ScatteredDrifter/Buran-Ortho/images/top-options/buran_top_filled.PNG

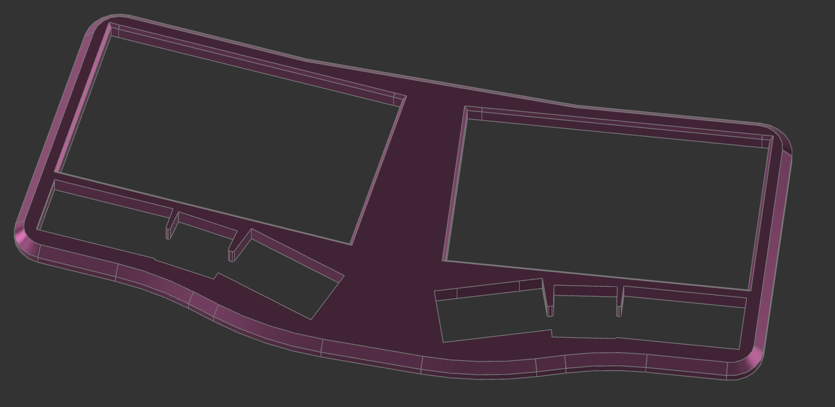
images/top-options/buran_top_filled.PNG
