ScatteredDrifter/Buran-Ortho/pcb/knobdeavour.kicad_sch

## KiCad design pcb/knobdeavour.kicad_sch (2022-11-30)

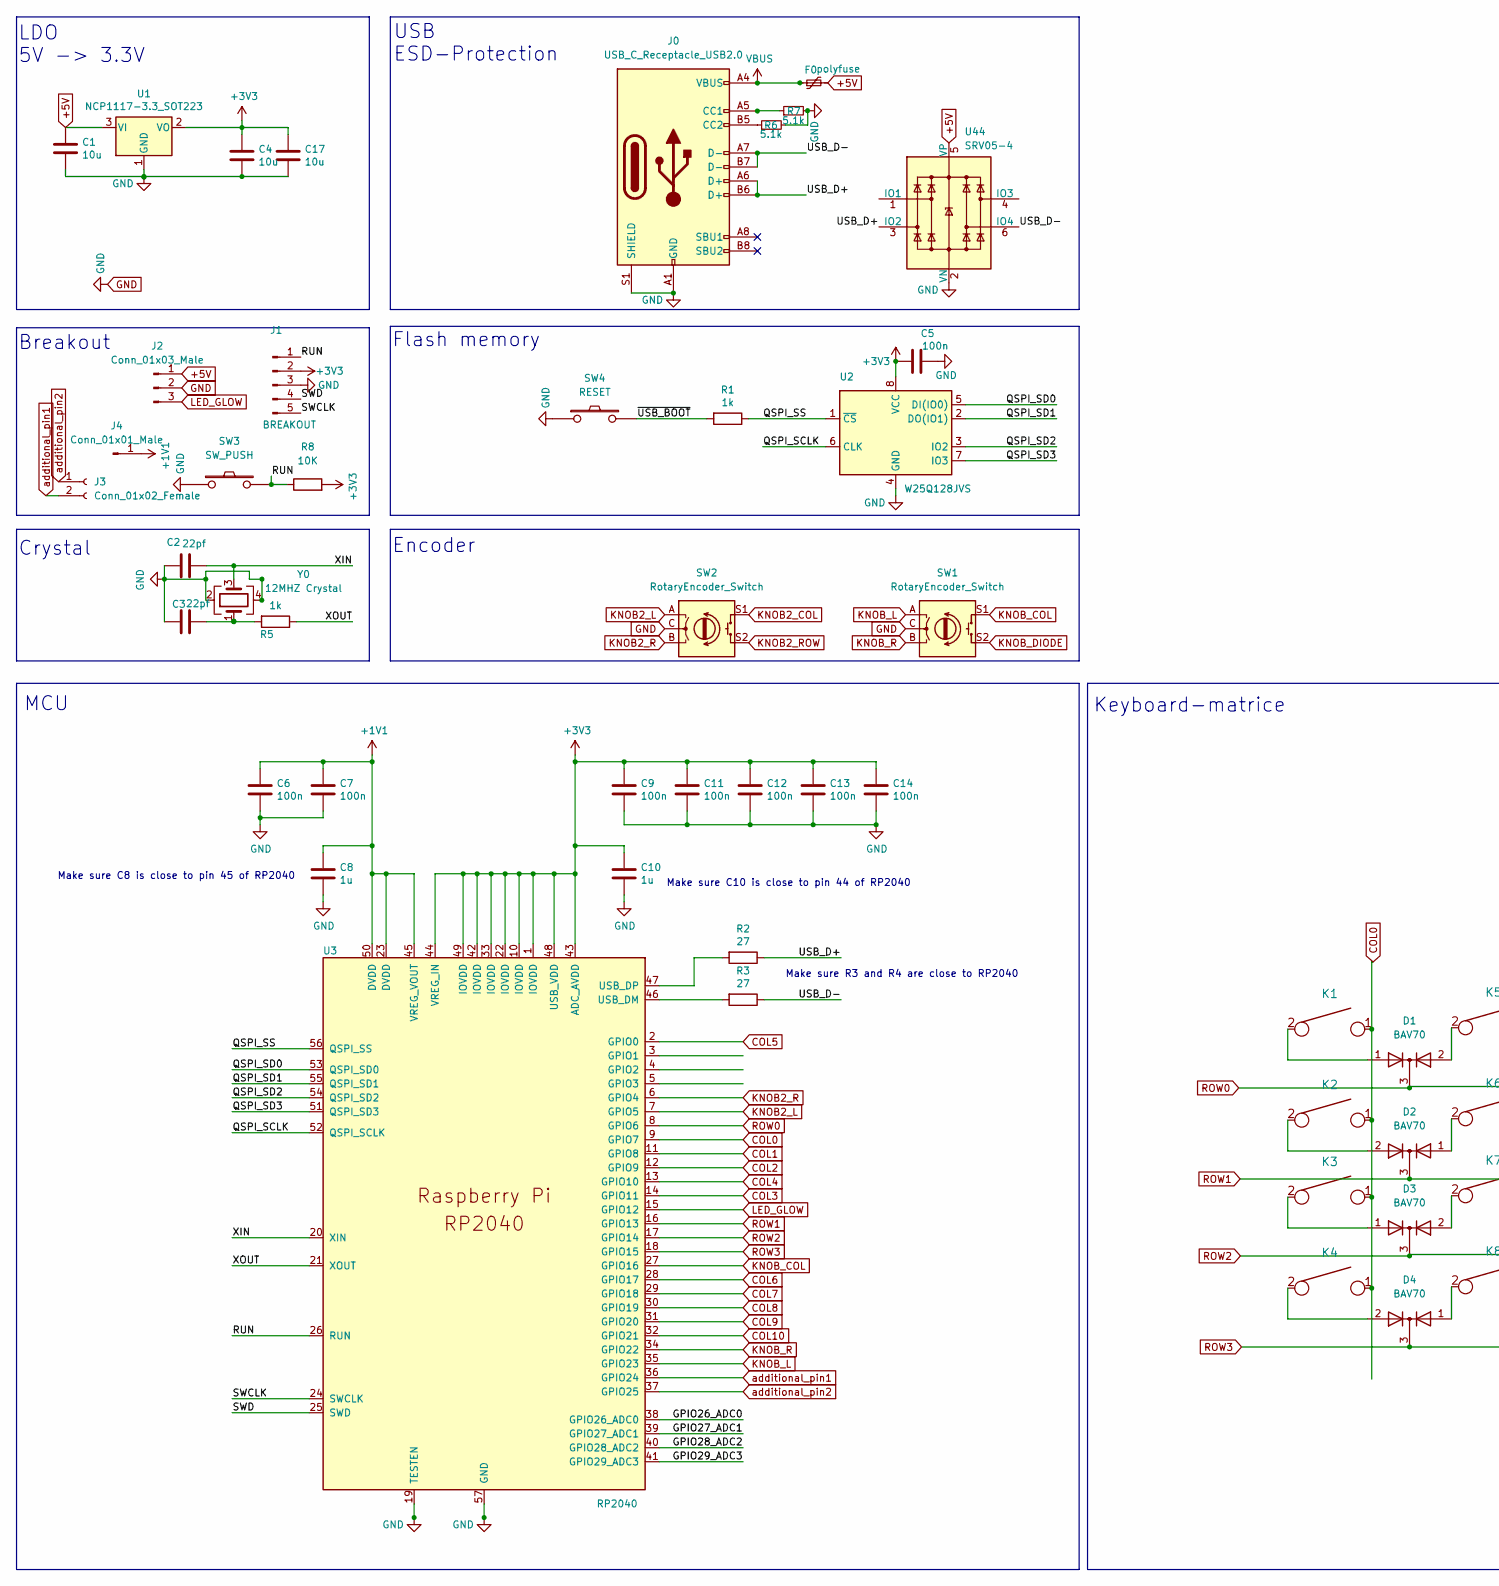
[picture p26: schematic knobdeavour.kicad_sch, part in row 1, column 1]

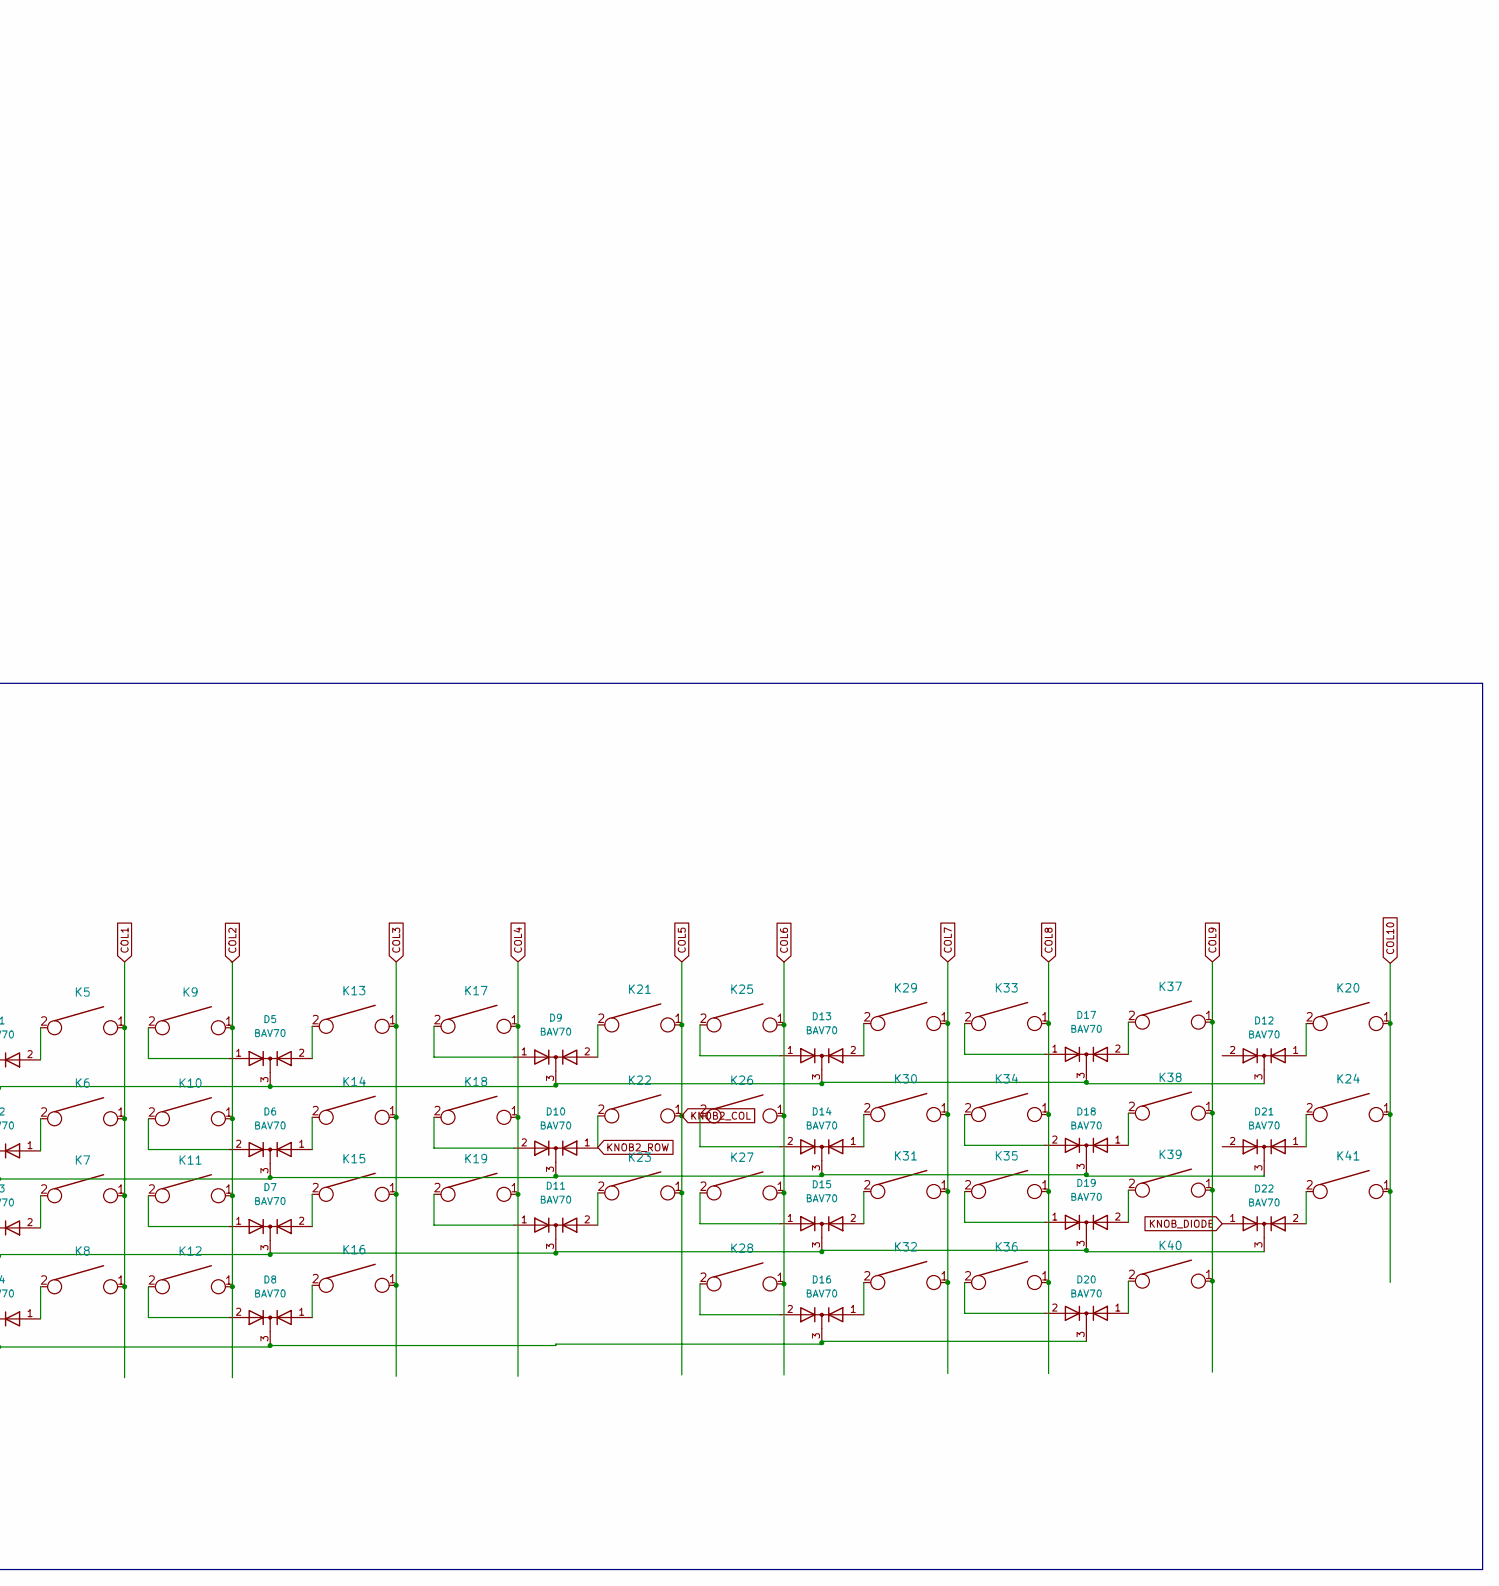
[picture p27: schematic knobdeavour.kicad_sch, part in row 1, column 2]

Parts:
C1, C4, C17: 10u; C_0805_2012Metric; LCSC C91245
C2, C3: 22pf; C_0805_2012Metric; LCSC C1804
C5, C6, C7, C9, C11, C12, C13, C14: 100n; C_0805_2012Metric; LCSC C49678
C8, C10: 1u; C_0805_2012Metric; LCSC C28323
D1, D2, D3, D4, D5, D6, D7, D8, D9, D10, D11, D12, D13, D14, D15, D16, D17, D18, D19, D20, D21, D22: BAV70; SOT-23; LCSC C68978
F0: polyfuse; Fuse_1206_3216Metric; LCSC C69688
J0: USB_C_Receptacle_USB2.0; USB_C_Receptacle_HRO_TYPE-C-31-M-12; LCSC C165948
J1: BREAKOUT; PinSocket_1x05_P2.54mm_Vertical
J2: Conn_01x03_Male; PinSocket_1x03_P2.54mm_Vertical
J3: Conn_01x02_Female; PinSocket_1x02_P2.54mm_Vertical
J4: Conn_01x01_Male; PinSocket_1x01_P1.27mm_Vertical
K1, K2, K3, K4, K5, K6, K7, K8, K9, K10, K11, K12, K13, K14, K15, K16, K17, K18, K19, K20, K21, K22, K23, K24, K25, K26, K27, K28, K29, K30, K31, K32, K33, K34, K35, K36, K37, K38, K39, K40, K41: KEYSW; MX-Alps-Choc-1U-NoLED
R1, R5: 1k; R_0805_2012Metric; LCSC C115316
R2, R3: 27; R_0805_2012Metric; LCSC C104170
R6, R7: 5.1k; R_0805_2012Metric; LCSC C27834
R8: 10K; R_0805_2012Metric; LCSC C115309
SW1, SW2: RotaryEncoder_Switch; RotaryEncoder_EC11
SW3: SW_PUSH; SW_SPST_TL3342; LCSC C318884
SW4: RESET; SW_SPST_TL3342; LCSC C318884
U1: NCP1117-3.3_SOT223; SOT-223-3_TabPin2; LCSC C26537
U2: W25Q128JVS; SOIC-8_5.23x5.23mm_P1.27mm; LCSC C97521
U3: RP2040; RP2040-QFN-56; LCSC C2040
U44: SRV05-4; SOT-23-6; LCSC C85364
Y0: 12MHZ Crystal; Crystal_SMD_3225-4Pin_3.2x2.5mm; LCSC C9002

Connections:
+1V1: C6.1, C7.1, C8.1, J4.1, U3.23 (DVDD), U3.45 (VREG_VOUT), U3.50 (DVDD)
+3V3: C4.1, C5.1, C9.1, C10.1, C11.1, C12.1, C13.1, C14.1, C17.1, J1.2, R8.2, U1.2 (VO), U2.8 (VCC), U3.1 (IOVDD), U3.10 (IOVDD), U3.22 (IOVDD), U3.33 (IOVDD), U3.42 (IOVDD), U3.43 (ADC_AVDD), U3.44 (VREG_IN), U3.48 (USB_VDD), U3.49 (IOVDD)
+5V: C1.1, F0.2, J2.1, U1.3 (VI), U44.5 (VP)
COL0: K1.1, K2.1, K3.1, K4.1, U3.9 (GPIO7)
COL1: K5.1, K6.1, K7.1, K8.1, U3.11 (GPIO8)
COL2: K9.1, K10.1, K11.1, K12.1, U3.12 (GPIO9)
COL3: K13.1, K14.1, K15.1, K16.1, U3.14 (GPIO11)
COL4: K17.1, K18.1, K19.1, U3.13 (GPIO10)
COL5: K21.1, K22.1, K23.1, SW2.S1, U3.2 (GPIO0)
COL6: K25.1, K26.1, K27.1, K28.1, U3.28 (GPIO17)
COL7: K29.1, K30.1, K31.1, K32.1, U3.29 (GPIO18)
COL8: K33.1, K34.1, K35.1, K36.1, U3.30 (GPIO19)
COL9: K37.1, K38.1, K39.1, K40.1, U3.31 (GPIO20)
COL10: K20.1, K24.1, K41.1, U3.32 (GPIO21)
GND: C1.2, C2.2, C3.2, C4.2, C5.2, C6.2, C7.2, C8.2, C9.2, C10.2, C11.2, C12.2, C13.2, C14.2, C17.2, J0.A1 (GND), J0.A12 (GND), J0.B1 (GND), J0.B12 (GND), J0.S1 (SHIELD), J1.3, J2.2, R6.2, R7.2, SW1.C, SW2.C, SW3.1, SW4.1, U1.1 (GND), U2.4 (GND), U3.19 (TESTEN), U3.57 (GND), U44.2 (VN), Y0.2, Y0.4
GPIO26_ADC0: U3.38 (GPIO26_ADC0)
GPIO27_ADC1: U3.39 (GPIO27_ADC1)
GPIO28_ADC2: U3.40 (GPIO28_ADC2)
GPIO29_ADC3: U3.41 (GPIO29_ADC3)
KNOB2_L: SW2.A, U3.7 (GPIO5)
KNOB2_R: SW2.B, U3.6 (GPIO4)
KNOB2_ROW: D10.1 (A), K22.2, SW2.S2
KNOB_COL: SW1.S1, U3.27 (GPIO16)
KNOB_DIODE: D22.1 (A), SW1.S2
KNOB_L: SW1.A, U3.35 (GPIO23)
KNOB_R: SW1.B, U3.34 (GPIO22)
LED_GLOW: J2.3, U3.15 (GPIO12)
unnamed: C3.1, R5.2, Y0.1
unnamed: D1.1 (A), K1.2
unnamed: D1.2 (A), K5.2
unnamed: D2.1 (A), K6.2
unnamed: D2.2 (A), K2.2
unnamed: D3.1 (A), K3.2
unnamed: D3.2 (A), K7.2
unnamed: D4.1 (A), K8.2
unnamed: D4.2 (A), K4.2
unnamed: D5.1 (A), K9.2
unnamed: D5.2 (A), K13.2
unnamed: D6.1 (A), K14.2
unnamed: D6.2 (A), K10.2
unnamed: D7.1 (A), K11.2
unnamed: D7.2 (A), K15.2
unnamed: D8.1 (A), K16.2
unnamed: D8.2 (A), K12.2
unnamed: D9.1 (A), K17.2
unnamed: D9.2 (A), K21.2
unnamed: D10.2 (A), K18.2
unnamed: D11.1 (A), K19.2
unnamed: D11.2 (A), K23.2
unnamed: D12.1 (A), K20.2
unnamed: D13.1 (A), K25.2
unnamed: D13.2 (A), K29.2
unnamed: D14.1 (A), K30.2
unnamed: D14.2 (A), K26.2
unnamed: D15.1 (A), K27.2
unnamed: D15.2 (A), K31.2
unnamed: D16.1 (A), K32.2
unnamed: D16.2 (A), K28.2
unnamed: D17.1 (A), K33.2
unnamed: D17.2 (A), K37.2
unnamed: D18.1 (A), K38.2
unnamed: D18.2 (A), K34.2
unnamed: D19.1 (A), K35.2
unnamed: D19.2 (A), K39.2
unnamed: D20.1 (A), K40.2
unnamed: D20.2 (A), K36.2
unnamed: D21.1 (A), K24.2
unnamed: D22.2 (A), K41.2
unnamed: J0.A5 (CC1), R7.1
unnamed: J0.B5 (CC2), R6.1
unnamed: R2.2, U3.47 (USB_DP)
unnamed: R3.2, U3.46 (USB_DM)
QSPI_SCLK: U2.6 (CLK), U3.52 (QSPI_SCLK)
QSPI_SD0: U2.5 (DI(IO0)), U3.53 (QSPI_SD0)
QSPI_SD1: U2.2 (DO(IO1)), U3.55 (QSPI_SD1)
QSPI_SD2: U2.3 (IO2), U3.54 (QSPI_SD2)
QSPI_SD3: U2.7 (IO3), U3.51 (QSPI_SD3)
QSPI_SS: R1.1, U2.1 (~CS), U3.56 (QSPI_SS)
ROW0: D1.3 (K), D5.3 (K), D9.3 (K), D12.3 (K), D13.3 (K), D17.3 (K), U3.8 (GPIO6)
ROW1: D2.3 (K), D6.3 (K), D10.3 (K), D14.3 (K), D18.3 (K), D21.3 (K), U3.16 (GPIO13)
ROW2: D3.3 (K), D7.3 (K), D11.3 (K), D15.3 (K), D19.3 (K), D22.3 (K), U3.17 (GPIO14)
ROW3: D4.3 (K), D8.3 (K), D16.3 (K), D20.3 (K), U3.18 (GPIO15)
RUN: J1.1, R8.1, SW3.2, U3.26 (RUN)
SWCLK: J1.5, U3.24 (SWCLK)
SWD: J1.4, U3.25 (SWD)
USB_D+: J0.A6 (D+), J0.B6 (D+), R2.1, U44.3 (IO2)
USB_D-: J0.A7 (D-), J0.B7 (D-), R3.1, U44.6 (IO4)
VBUS: F0.1, J0.A4 (VBUS), J0.A9 (VBUS), J0.B4 (VBUS), J0.B9 (VBUS)
XIN: C2.1, U3.20 (XIN), Y0.3
XOUT: R5.1, U3.21 (XOUT)
additional_pin1: J3.2, U3.36 (GPIO24)
additional_pin2: J3.1, U3.37 (GPIO25)
~USB_BOOT: R1.2, SW4.2

Notes on the sheet:
Crystal
USB ESD-Protection
MCU
Flash memory
Breakout
LDO 5V -> 3.3V
Make sure R3 and R4 are close to RP2040
Make sure C8 is close to pin 45 of RP2040
Keyboard-matrice
Make sure C10 is close to pin 44 of RP2040
Encoder
