ScatteredDrifter/Buran-Ortho/firmware/vial/buran/keymaps/vial/config.h

/* SPDX-License-Identifier: GPL-2.0-or-later */

#pragma once

#define VIAL_KEYBOARD_UID {0x3F, 0x25, 0xD9, 0xFC, 0xA2, 0x98, 0x8F, 0x98}

#define DYNAMIC_KEYMAP_LAYER_COUNT 8

#define VIAL_UNLOCK_COMBO_ROWS { 1, 1 }
#define VIAL_UNLOCK_COMBO_COLS { 0, 10 }

#define ENCODERS_PAD_A {GP22, GP4}
#define ENCODERS_PAD_B {GP23, GP5}
